TychoBECH/microbench_psu/firmware/microbench_psu.X/mcp47cxdx.h

/* Microchip Technology Inc. and its subsidiaries.  You may use this software 
 * and any derivatives exclusively with Microchip products. 
 * 
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
 * IN NO EVENT WILL MICROCHIP BE LIABLE FOR ANY INDIRECT, SPECIAL, PUNITIVE, 
 * INCIDENTAL OR CONSEQUENTIAL LOSS, DAMAGE, COST OR EXPENSE OF ANY KIND 
 * WHATSOEVER RELATED TO THE SOFTWARE, HOWEVER CAUSED, EVEN IF MICROCHIP HAS 
 * BEEN ADVISED OF THE POSSIBILITY OR THE DAMAGES ARE FORESEEABLE.  TO THE 
 * FULLEST EXTENT ALLOWED BY LAW, MICROCHIP'S TOTAL LIABILITY ON ALL CLAIMS 
 * IN ANY WAY RELATED TO THIS SOFTWARE WILL NOT EXCEED THE AMOUNT OF FEES, IF 
 * ANY, THAT YOU HAVE PAID DIRECTLY TO MICROCHIP FOR THIS SOFTWARE.
 *
 * MICROCHIP PROVIDES THIS SOFTWARE CONDITIONALLY UPON YOUR ACCEPTANCE OF THESE 
 * TERMS. 
 */

/* 
 * File:   
 * Author: 
 * Comments:
 * Revision history: 
 */

// This is a guard condition so that contents of this file are not included
// more than once.  
#ifndef MCP47CXDX_H
#define	MCP47CXDX_H

#include <xc.h> // include processor files - each processor file is guarded.  

// TODO Insert appropriate #include <>

// TODO Insert C++ class definitions if appropriate

// TODO Insert declarations
#define MCP47_I2C_Address 0b1100000

//Bits 7-3 are the address, bits 2-0 are the command
#define MCP47_DAC0_REGISTER_ADDRESS 0x00
#define MCP47_DAC1_REGISTER_ADDRESS 0b00001000
#define MCP47_VREF_REGISTER_ADDRESS 0b01000000
#define MCP47_PD0_REGISTER_ADDRESS 0b01001000

typedef enum {
	MCP47_CHANNEL_0 = 0,
	MCP47_CHANNEL_1 = 1
} MCP47_CANNEL_t;

// Comment a function and leverage automatic documentation with slash star star
/**
	<p><b>Function prototype:</b></p>
  
	<p><b>Summary:</b></p>

	<p><b>Description:</b></p>

	<p><b>Precondition:</b></p>

	<p><b>Parameters:</b></p>

	<p><b>Returns:</b></p>

	<p><b>Example:</b></p>
	<code>
 
	</code>

	<p><b>Remarks:</b></p>
 */
void MCP47_SetOutput(MCP47_CANNEL_t channel, uint16_t value);

#ifdef	__cplusplus
extern "C" {
#endif /* __cplusplus */

	// TODO If C++ is being used, regular C code needs function names to have C 
	// linkage so the functions can be used by the c code. 

#ifdef	__cplusplus
}
#endif /* __cplusplus */

#endif	/* XC_HEADER_TEMPLATE_H */
